JendrikBot/Slimme-Projector/img/afbeelding storyboard develop 1.JPEG

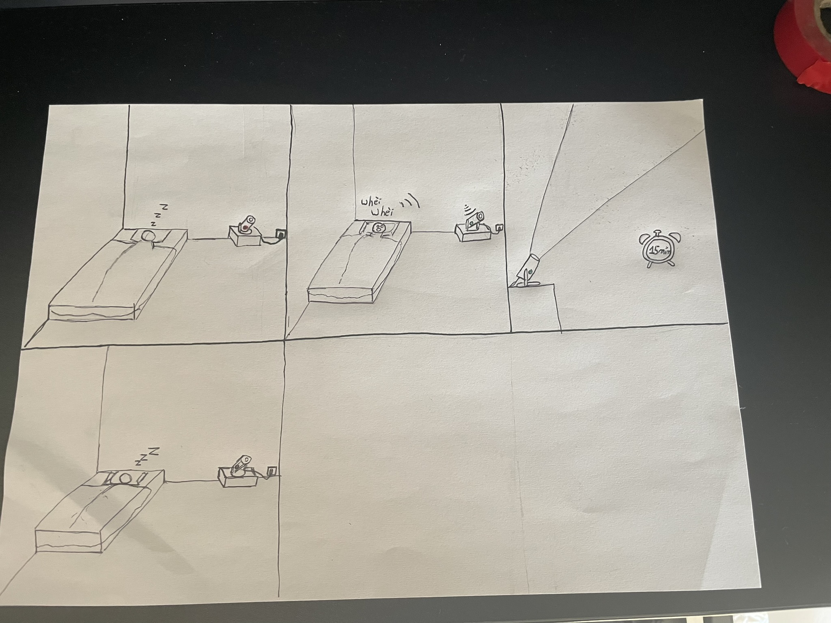
img/afbeelding storyboard develop 1.JPEG
