JendrikBot/Slimme-Projector/img/afbeelding_samenstelling_1.JPEG

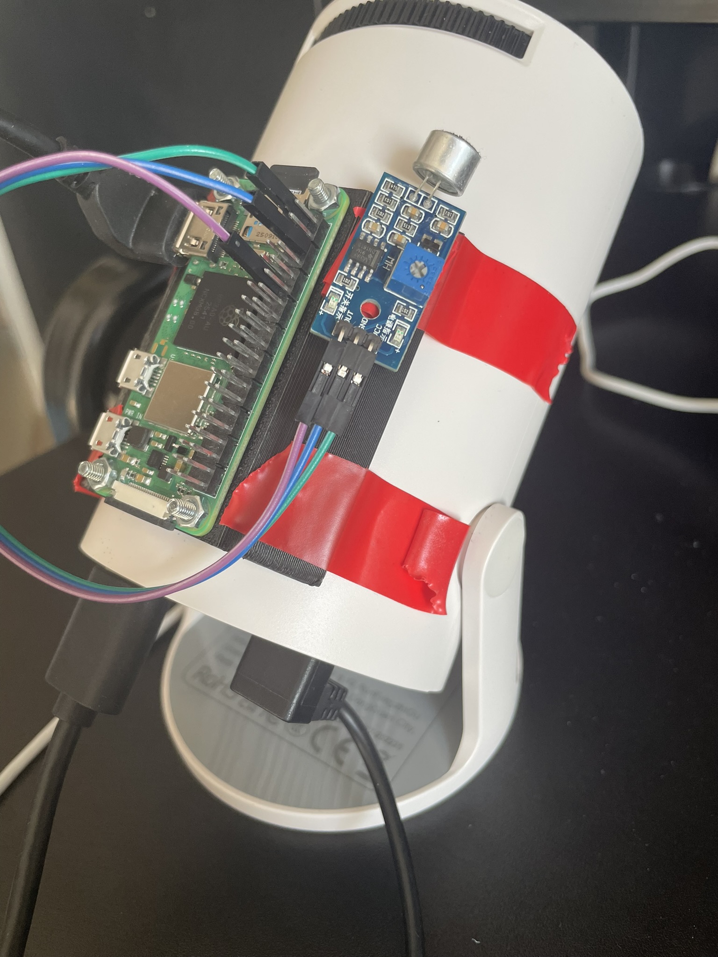
img/afbeelding_samenstelling_1.JPEG
