JendrikBot/Slimme-Projector/img/Bottelberghe_Jendrik_render_Slimme-Projector.png

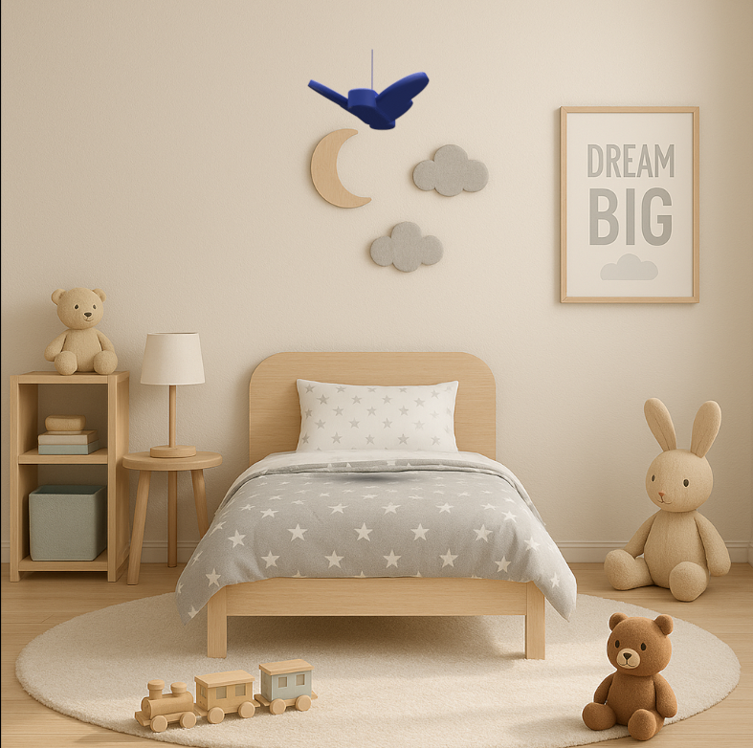
img/Bottelberghe_Jendrik_render_Slimme-Projector.png
