JendrikBot/Slimme-Projector/img/Bottelberghe_Jendrik_storyboard.jpeg

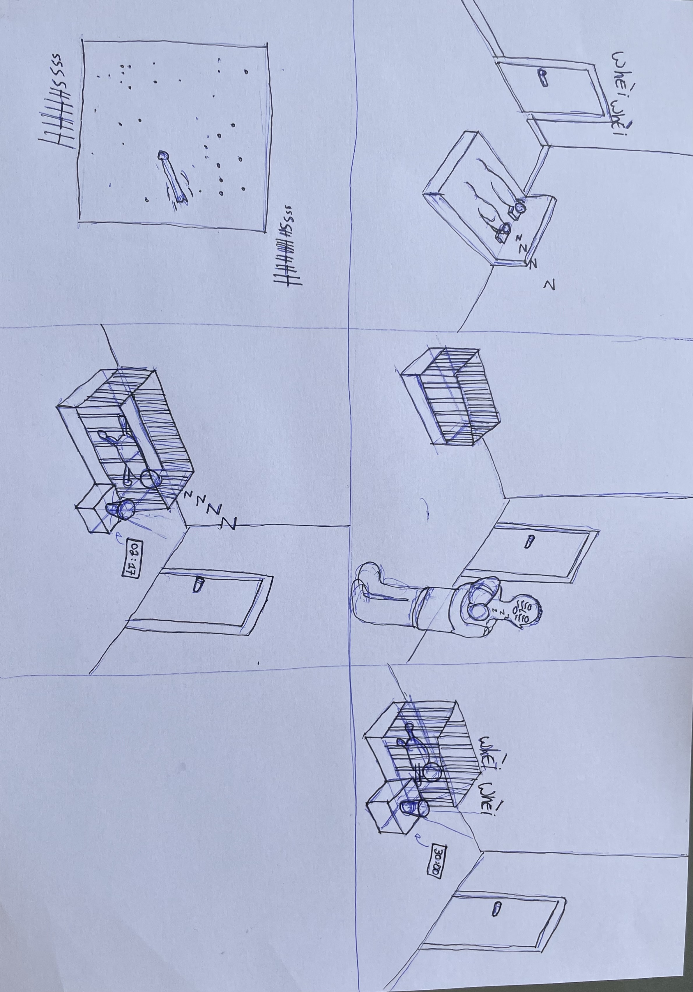
img/Bottelberghe_Jendrik_storyboard.jpeg
