JendrikBot/Slimme-Projector/img/develop_2_prototype.JPEG

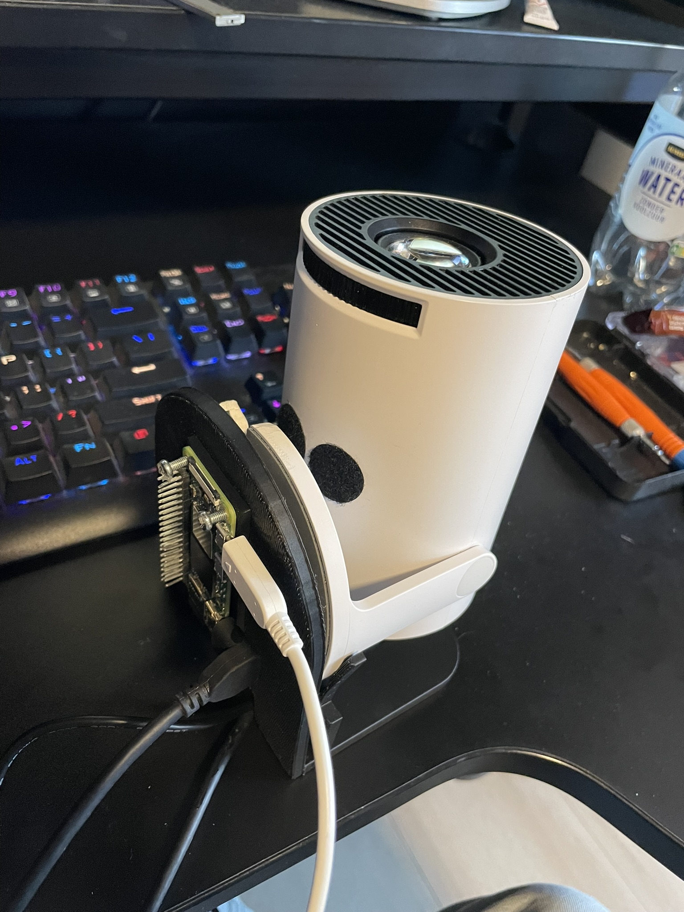
img/develop_2_prototype.JPEG
