JendrikBot/Slimme-Projector/img/HPI.jpg

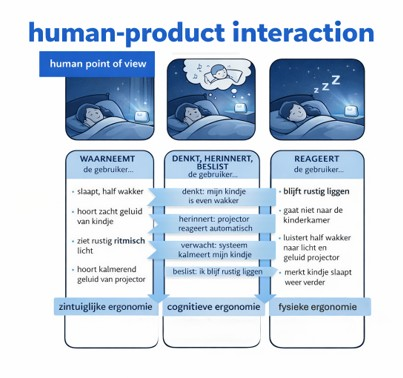
img/HPI.jpg
