JendrikBot/Slimme-Projector/img/model_NX_JB.png

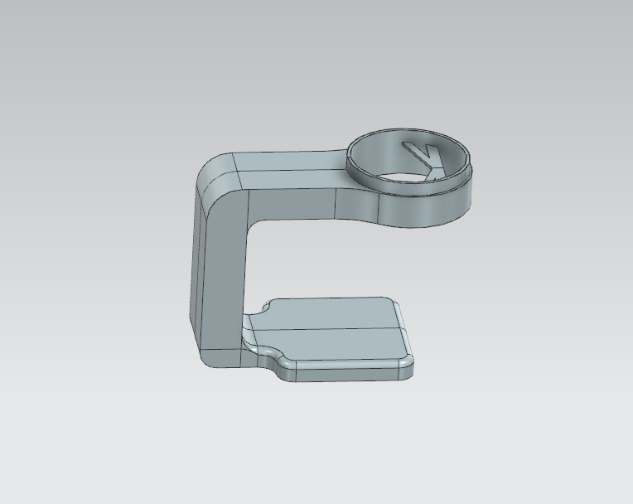
img/model_NX_JB.png
