JendrikBot/Slimme-Projector/img/render_slimme_projector.png

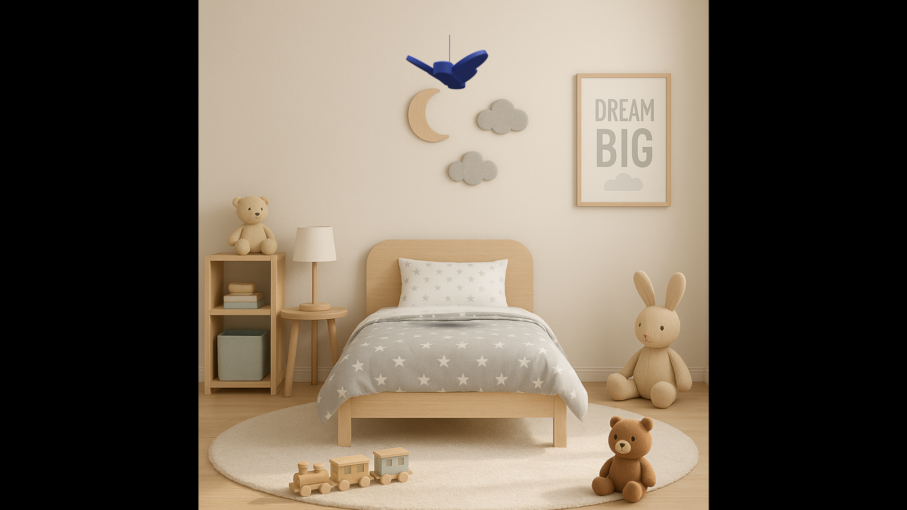
img/render_slimme_projector.png
