JendrikBot/Slimme-Projector/img/schets_develop3.1_ JB.JPEG

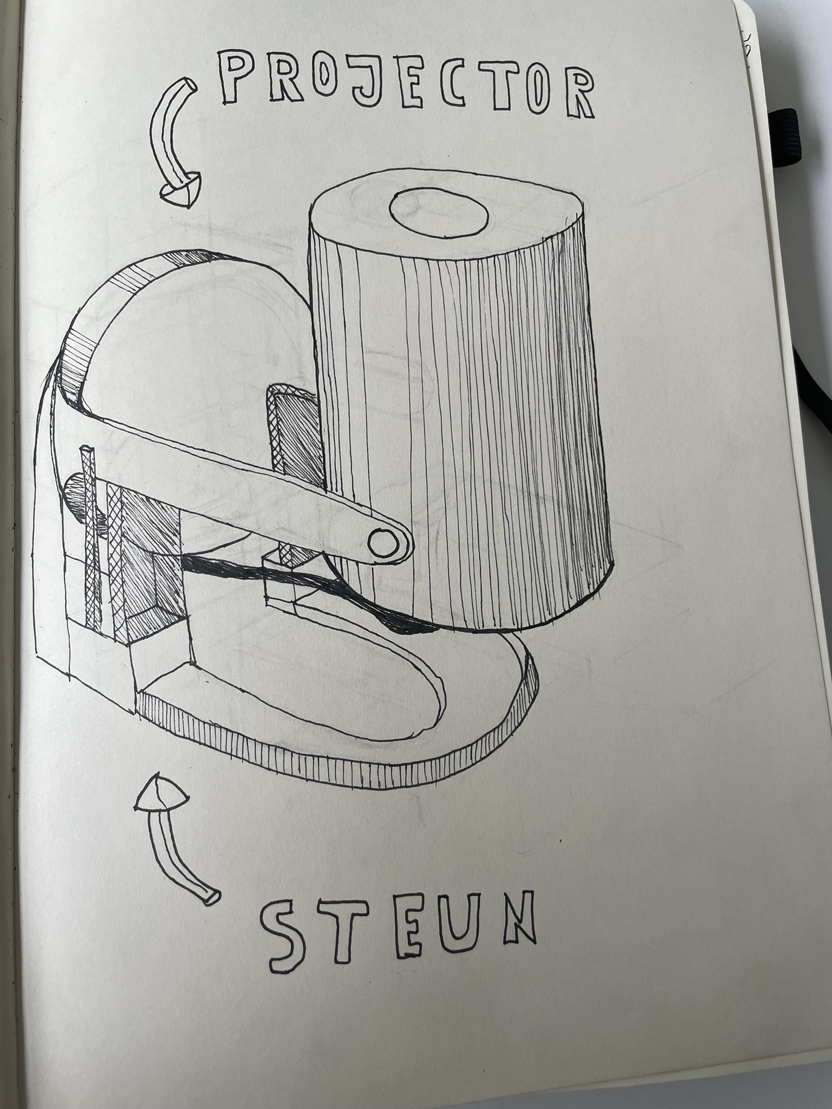
img/schets_develop3.1_ JB.JPEG
