JendrikBot/Slimme-Projector/img/schets_develop3.2_JB.JPEG

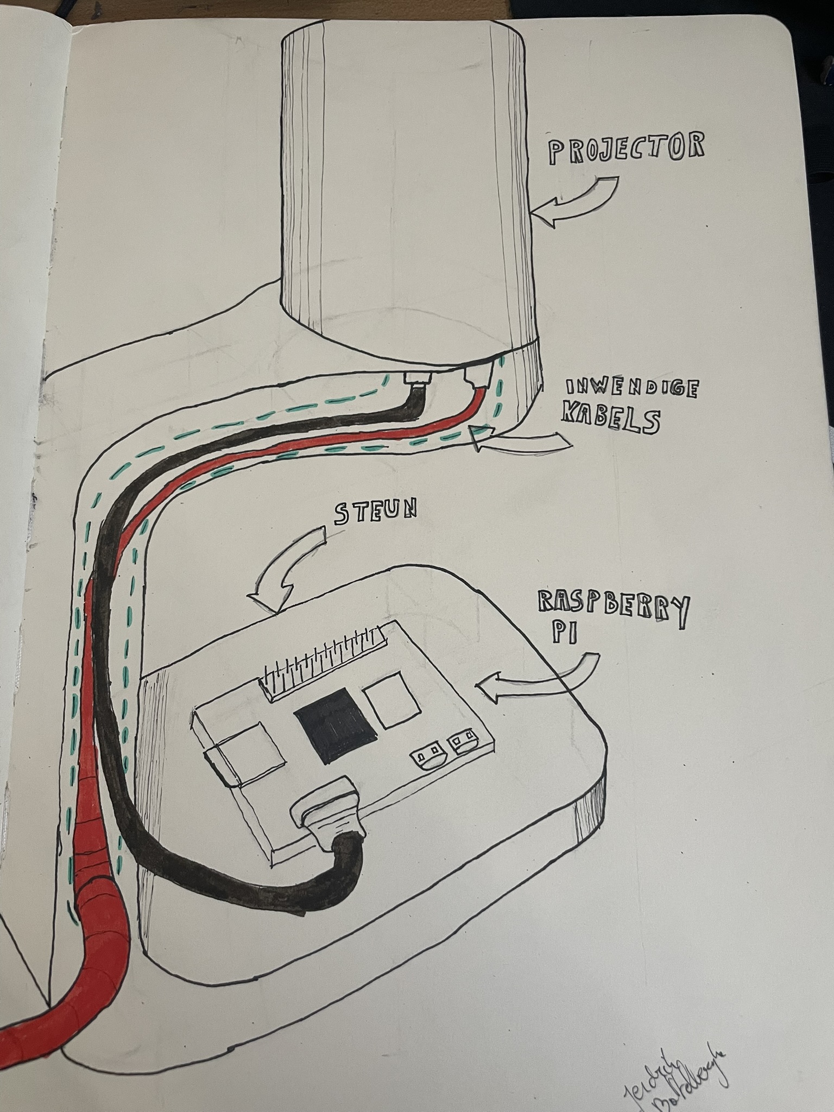
img/schets_develop3.2_JB.JPEG
