JendrikBot/Slimme-Projector/img/seven_stages_of_action.png

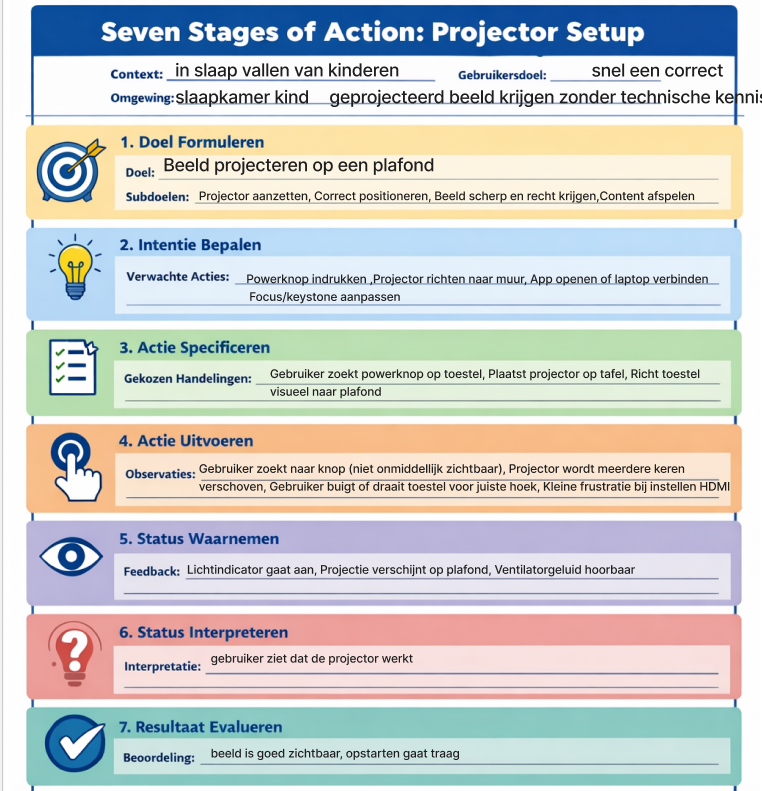
img/seven_stages_of_action.png
