JendrikBot/Slimme-Projector/img/userflow_develop_1.jpg

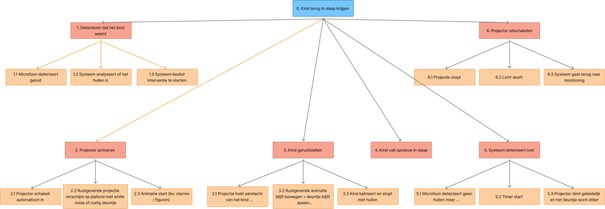
img/userflow_develop_1.jpg
