JendrikBot/Slimme-Projector/img/Vanhoutte_Felix_storyboard.jpeg

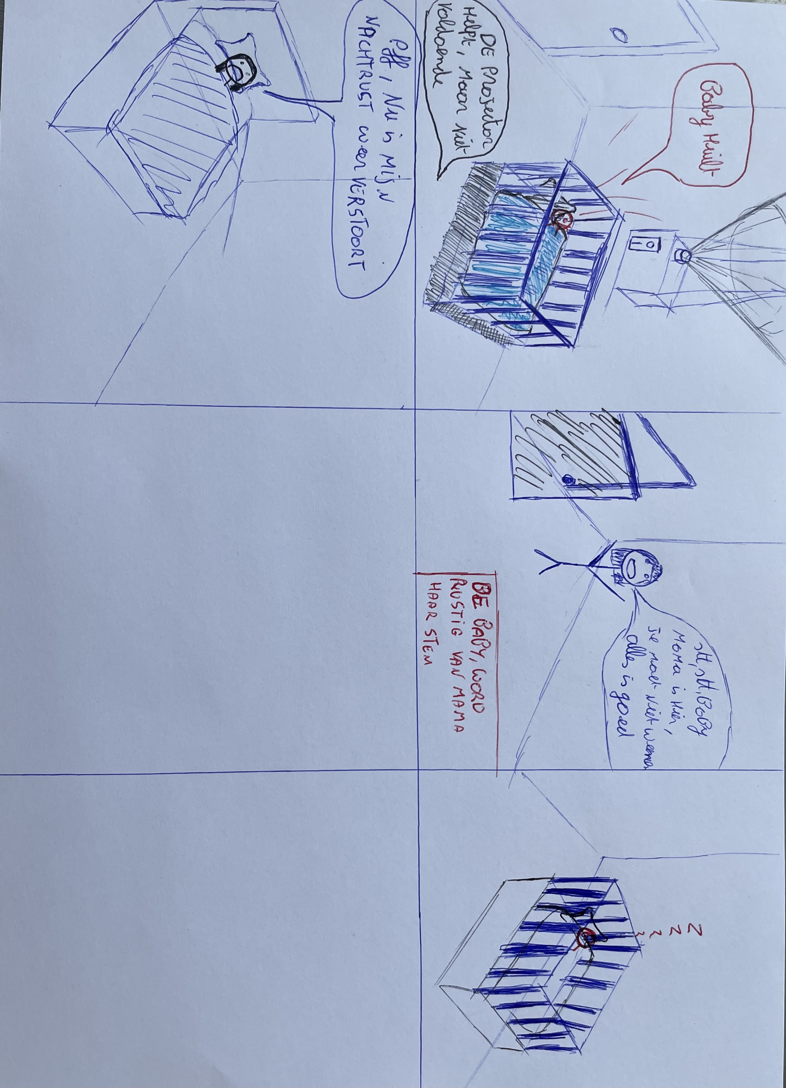
img/Vanhoutte_Felix_storyboard.jpeg
